simium/Koroliov/Software/Koroliov_Main/rs8encode.c

/* Reed-Solomon encoder
 * Copyright 2004, Phil Karn, KA9Q
 * May be used under the terms of the GNU Lesser General Public License (LGPL)
 */

#include "config.h"
#include <string.h>
#include <avr/pgmspace.h>
#include "rs8.h"

#define MM     (8)
#define NN     (255)
#define NROOTS (32)
#define FCR    (112)
#define PRIM   (11)
#define IPRIM  (116)

#define MIN(a,b) ((a) < (b) ? (a) : (b))
#define A0       (NN) /* Special reserved value encoding zero in index form */

inline int mod255(int x)
{
  while(x >= 255)
  {
    x -= 255;
    x = (x >> 8) + (x & 255);
  }
  return(x);
}

PROGMEM const uint8_t alpha_to[] = {
  0x01,0x02,0x04,0x08,0x10,0x20,0x40,0x80,0x87,0x89,0x95,0xAD,0xDD,0x3D,0x7A,0xF4,
  0x6F,0xDE,0x3B,0x76,0xEC,0x5F,0xBE,0xFB,0x71,0xE2,0x43,0x86,0x8B,0x91,0xA5,0xCD,
  0x1D,0x3A,0x74,0xE8,0x57,0xAE,0xDB,0x31,0x62,0xC4,0x0F,0x1E,0x3C,0x78,0xF0,0x67,
  0xCE,0x1B,0x36,0x6C,0xD8,0x37,0x6E,0xDC,0x3F,0x7E,0xFC,0x7F,0xFE,0x7B,0xF6,0x6B,
  0xD6,0x2B,0x56,0xAC,0xDF,0x39,0x72,0xE4,0x4F,0x9E,0xBB,0xF1,0x65,0xCA,0x13,0x26,
  0x4C,0x98,0xB7,0xE9,0x55,0xAA,0xD3,0x21,0x42,0x84,0x8F,0x99,0xB5,0xED,0x5D,0xBA,
  0xF3,0x61,0xC2,0x03,0x06,0x0C,0x18,0x30,0x60,0xC0,0x07,0x0E,0x1C,0x38,0x70,0xE0,
  0x47,0x8E,0x9B,0xB1,0xE5,0x4D,0x9A,0xB3,0xE1,0x45,0x8A,0x93,0xA1,0xC5,0x0D,0x1A,
  0x34,0x68,0xD0,0x27,0x4E,0x9C,0xBF,0xF9,0x75,0xEA,0x53,0xA6,0xCB,0x11,0x22,0x44,
  0x88,0x97,0xA9,0xD5,0x2D,0x5A,0xB4,0xEF,0x59,0xB2,0xE3,0x41,0x82,0x83,0x81,0x85,
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
    }

    /* Shift */
    memmove(&parity[0], &parity[1], sizeof(uint8_t) * (NROOTS - 1));
    if(feedback != A0)
      parity[NROOTS - 1] = pgm_read_byte(&alpha_to[mod255(feedback + pgm_read_byte(&poly[0]))]);
    else
      parity[NROOTS - 1] = 0;
  }
}
